fitch/SVI-328-PicoROM/pico/c/rom.h

unsigned char ROM[] = {
  0xf3, 0x31, 0x1c, 0xf2, 0x21, 0x12, 0x00, 0x11, 0x00, 0xc0, 0x01, 0x7d,
  0x03, 0xed, 0xb0, 0xc3, 0x00, 0xc0, 0xcd, 0x55, 0xc3, 0xcd, 0x8e, 0xc2,
  0xcd, 0x86, 0x3b, 0xcd, 0x41, 0x35, 0xc3, 0xae, 0xc0, 0xcd, 0x55, 0xc3,
  0x21, 0xde, 0xc0, 0xcd, 0x85, 0xc2, 0x21, 0xf8, 0xc1, 0x06, 0x20, 0xcd,
  0x4f, 0xc2, 0x21, 0x0b, 0xc1, 0xcd, 0x85, 0xc2, 0x21, 0x18, 0xc2, 0x06,
  0x20, 0xcd, 0x4f, 0xc2, 0x21, 0x1b, 0xc1, 0xcd, 0x85, 0xc2, 0xcd, 0x61,
  0xc3, 0xcd, 0x38, 0xc2, 0x3a, 0x00, 0x7f, 0x21, 0xf8, 0xc1, 0x01, 0x20,
  0x00, 0xcd, 0x45, 0xc2, 0xcd, 0x38, 0xc2, 0x3a, 0x02, 0x7f, 0xcd, 0x38,
  0xc2, 0x3a, 0x01, 0x7f, 0x21, 0x18, 0xc2, 0x01, 0x20, 0x00, 0xcd, 0x45,
  0xc2, 0xcd, 0x38, 0xc2, 0x3a, 0x02, 0x7f, 0xc3, 0xae, 0xc0, 0xcd, 0x55,
  0xc3, 0x21, 0x38, 0xc1, 0xcd, 0x85, 0xc2, 0xc3, 0xae, 0xc0, 0xcd, 0x55,
  0xc3, 0x21, 0x4e, 0xc1, 0xcd, 0x85, 0xc2, 0xc3, 0xae, 0xc0, 0xcd, 0x55,
  0xc3, 0x21, 0x67, 0xc1, 0xcd, 0x85, 0xc2, 0xc3, 0xae, 0xc0, 0xcd, 0x55,
  0xc3, 0x21, 0x8c, 0xc1, 0xcd, 0x85, 0xc2, 0xc3, 0xae, 0xc0, 0xcd, 0x55,
  0xc3, 0x21, 0xb5, 0xc1, 0xcd, 0x85, 0xc2, 0xcd, 0x61, 0xc3, 0xc3, 0x00,
  0x00, 0xcd, 0x55, 0xc3, 0x21, 0xcd, 0xc1, 0xcd, 0x85, 0xc2, 0x18, 0xfe,
  0xcd, 0x61, 0xc3, 0x3a, 0xff, 0x7f, 0x47, 0x3a, 0xf7, 0xc1, 0xb8, 0x28,
  0xf6, 0x78, 0x32, 0xf7, 0xc1, 0xfe, 0x64, 0xca, 0x0f, 0xc0, 0xfe, 0x65,
  0x28, 0x9c, 0xfe, 0x67, 0x28, 0xa4, 0xfe, 0x68, 0x28, 0xac, 0xfe, 0x69,
  0x28, 0xcf, 0xfe, 0x6a, 0x28, 0xb0, 0xfe, 0x6c, 0x28, 0xb8, 0x18, 0xd3,
  0x4c, 0x65, 0x74, 0x27, 0x73, 0x20, 0x63, 0x6f, 0x6e, 0x6e, 0x65, 0x63,
  0x74, 0x20, 0x79, 0x6f, 0x75, 0x20, 0x74, 0x6f, 0x20, 0x57, 0x69, 0x2d,
  0x46, 0x69, 0x20, 0x66, 0x69, 0x72, 0x73, 0x74, 0x2e, 0x0d, 0x0a, 0x0d,
  0x0a, 0x53, 0x53, 0x49, 0x44, 0x3a, 0x0d, 0x0a, 0x00, 0x0d, 0x0a, 0x0d,
  0x0a, 0x50, 0x61, 0x73, 0x73, 0x77, 0x6f, 0x72, 0x64, 0x3a, 0x0d, 0x0a,
  0x00, 0x0d, 0x0a, 0x0d, 0x0a, 0x53, 0x74, 0x6f, 0x72, 0x69, 0x6e, 0x67,
  0x20, 0x63, 0x72, 0x65, 0x64, 0x65, 0x6e, 0x74, 0x69, 0x61, 0x6c, 0x73,
  0x2e, 0x2e, 0x2e, 0x0d, 0x0a, 0x00, 0x43, 0x72, 0x65, 0x64, 0x65, 0x6e,
  0x74, 0x69, 0x61, 0x6c, 0x73, 0x20, 0x73, 0x74, 0x6f, 0x72, 0x65, 0x64,
  0x2e, 0x0d, 0x0a, 0x00, 0x43, 0x6f, 0x6e, 0x6e, 0x65, 0x63, 0x74, 0x69,
  0x6e, 0x67, 0x20, 0x74, 0x6f, 0x20, 0x57, 0x69, 0x2d, 0x46, 0x69, 0x2e,
  0x2e, 0x2e, 0x0d, 0x0a, 0x00, 0x43, 0x6f, 0x6e, 0x6e, 0x65, 0x63, 0x74,
  0x65, 0x64, 0x2c, 0x20, 0x77, 0x61, 0x69, 0x74, 0x69, 0x6e, 0x67, 0x20,
  0x66, 0x6f, 0x72, 0x20, 0x61, 0x20, 0x63, 0x6c, 0x69, 0x65, 0x6e, 0x74,
  0x2e, 0x2e, 0x2e, 0x0d, 0x0a, 0x00, 0x43, 0x6c, 0x69, 0x65, 0x6e, 0x74,
  0x20, 0x63, 0x6f, 0x6e, 0x6e, 0x65, 0x63, 0x74, 0x65, 0x64, 0x2c, 0x20,
  0x77, 0x61, 0x69, 0x74, 0x69, 0x6e, 0x67, 0x20, 0x66, 0x6f, 0x72, 0x20,
  0x61, 0x20, 0x52, 0x4f, 0x4d, 0x2e, 0x2e, 0x2e, 0x0d, 0x0a, 0x00, 0x52,
  0x4f, 0x4d, 0x20, 0x72, 0x65, 0x61, 0x64, 0x79, 0x2c, 0x20, 0x62, 0x6f,
  0x6f, 0x74, 0x69, 0x6e, 0x67, 0x2e, 0x2e, 0x2e, 0x0d, 0x0a, 0x00, 0x45,
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
};
unsigned int ROM_len = 32768;
